TinyCircuits/TinyCircuits-Wireling-TOF-AST1024/cad/Wireling_TOF_AST1024_REV2-DETAILED_DRAWING-PNG.png

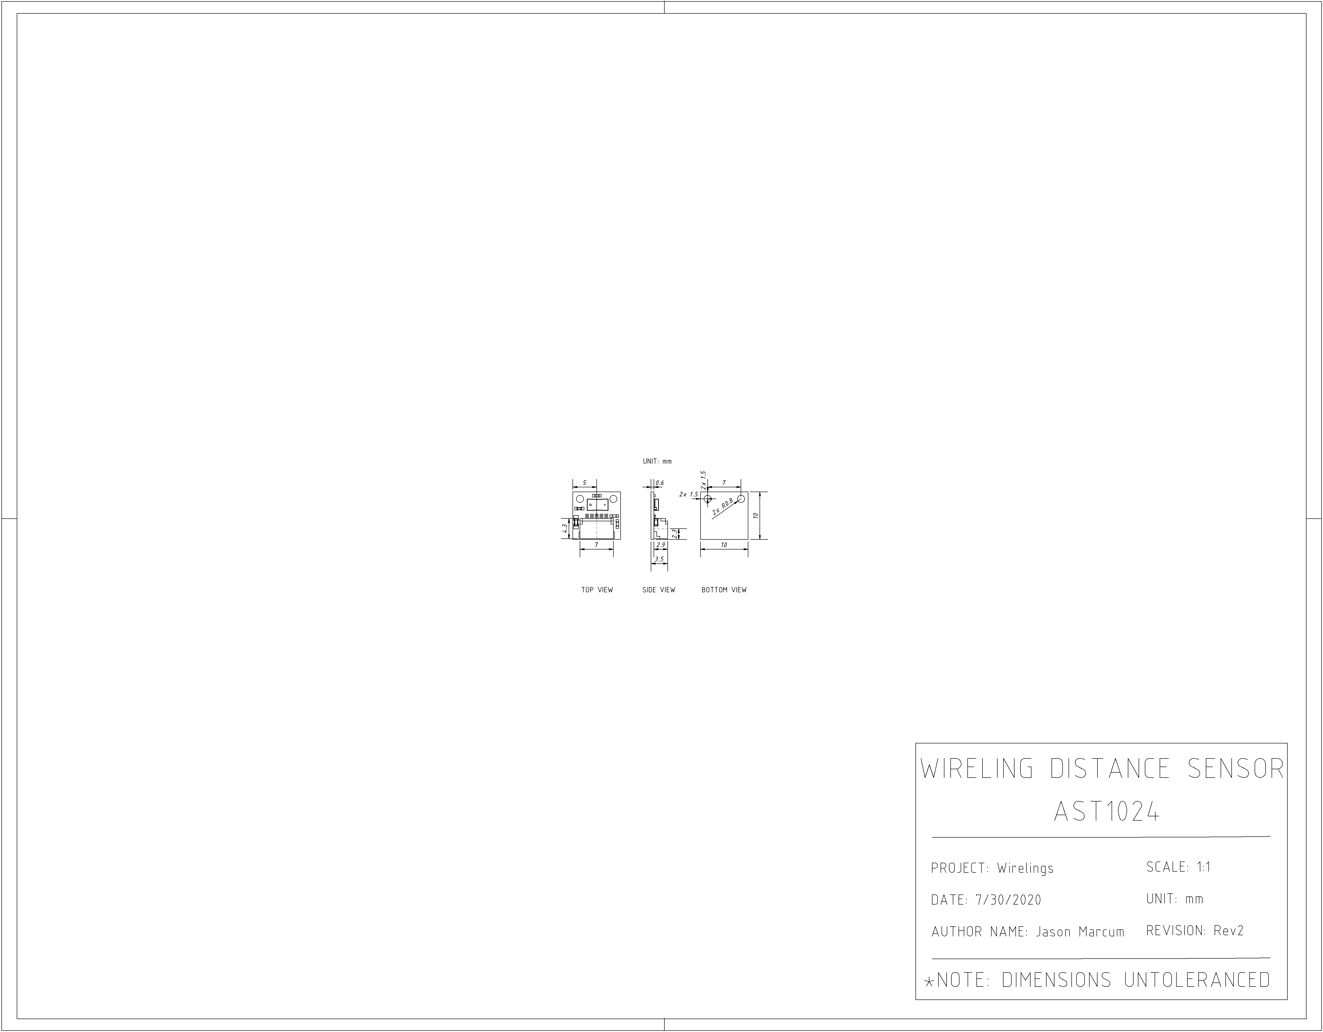
cad/Wireling_TOF_AST1024_REV2-DETAILED_DRAWING-PNG.png
