TinyCircuits/TinyCircuits-Wireling-TOF-AST1024/images/AST1024-Tutorial-Image-01.png

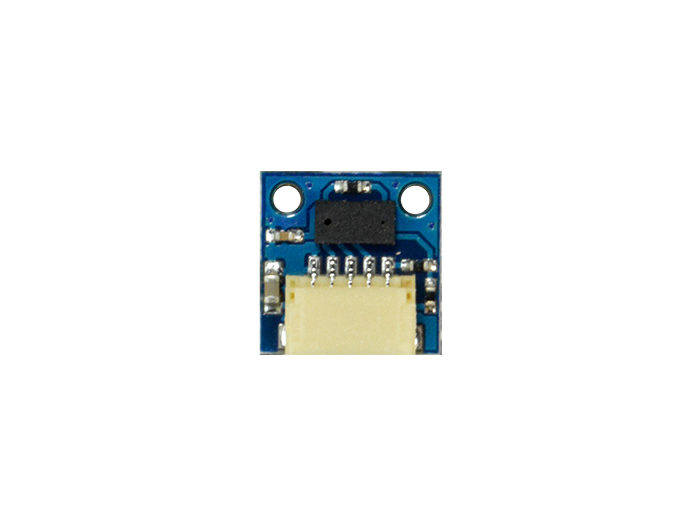
images/AST1024-Tutorial-Image-01.png
